CinTheDev/ThermalCamera/CAD_CaseV2/Parts/Casing2.FCStd

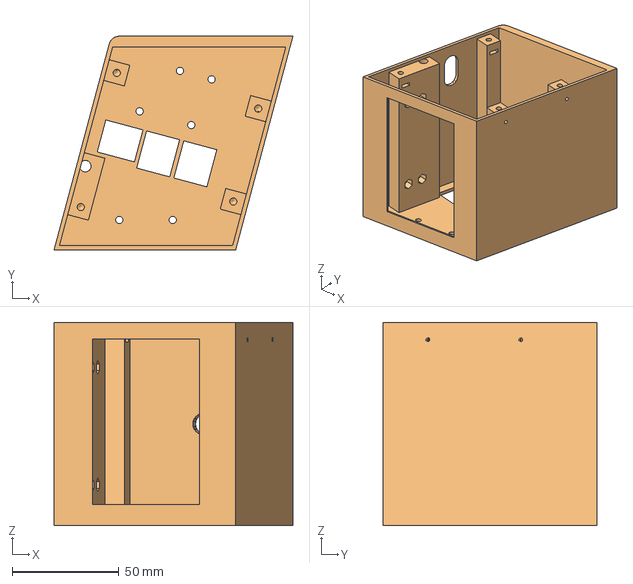
[picture p19: CAD file, 2023-12-11]
CAD_CaseV2/Parts/Casing2.FCStd
111.8 x 100.0 x 95.0 mm
Körper
Körper (Meshed)
