CinTheDev/ThermalCamera/CAD_CaseV2/Parts/MLX90640.FCStd

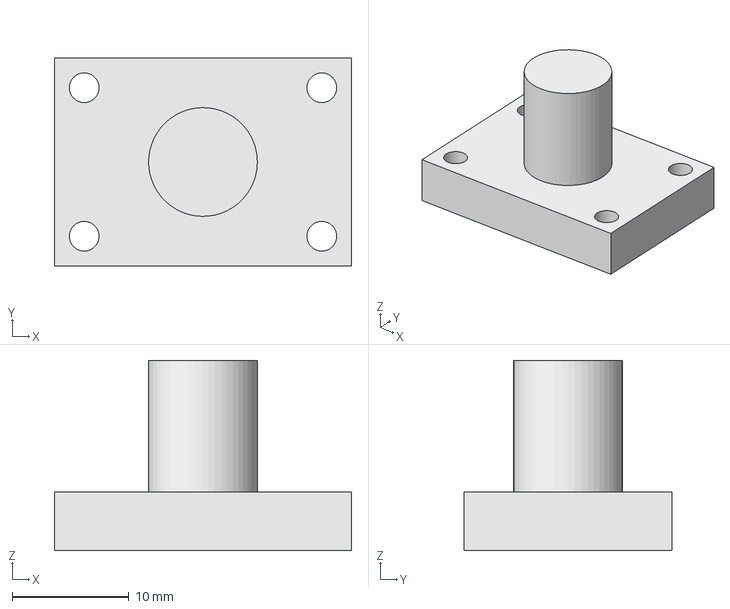
[picture p20: CAD file, 2023-12-11]
CAD_CaseV2/Parts/MLX90640.FCStd
25.4 x 17.8 x 16.2 mm
